sh123/arduino_uno_pet_puller/extras/cad_petalot/guide-base.stl

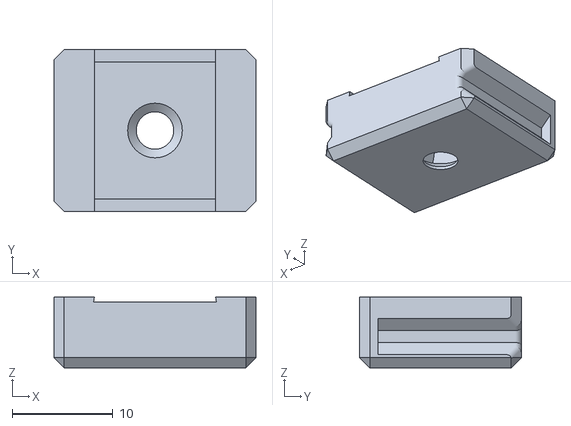
[picture p15: CAD file, 2025-09-10]
extras/cad_petalot/guide-base.stl
20.0 x 16.0 x 7.00
