sh123/arduino_uno_pet_puller/extras/cad_petalot/cable-clamp.stl

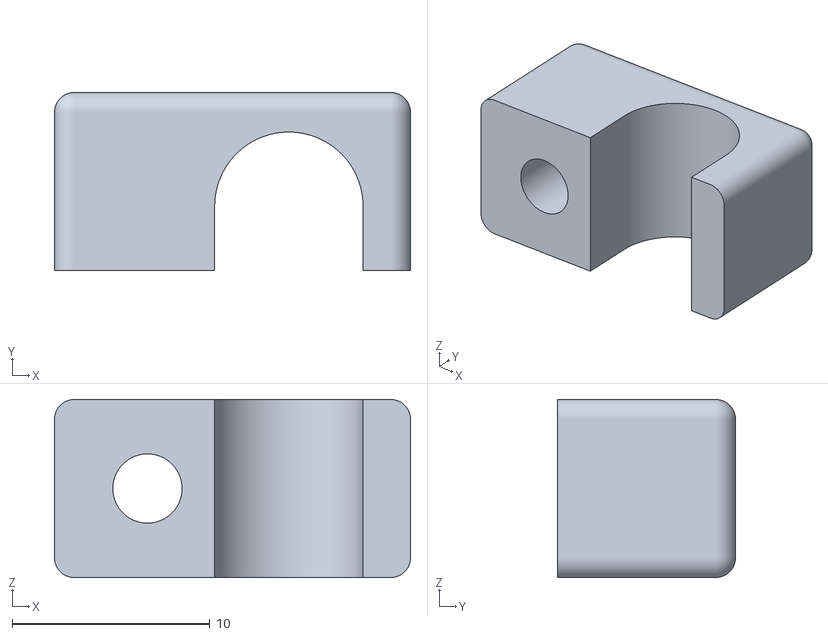
[picture p16: CAD file, 2025-09-10]
extras/cad_petalot/cable-clamp.stl
18.0 x 9.00 x 9.00
