sh123/arduino_uno_pet_puller/extras/cad_petalot/pulley.stl

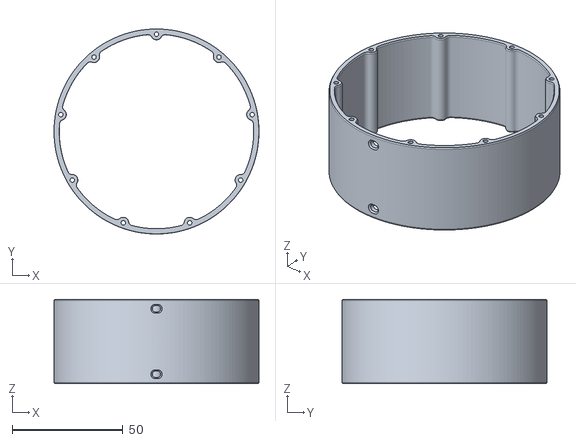
[picture p17: CAD file, 2025-09-10]
extras/cad_petalot/pulley.stl
92.4 x 92.4 x 38.0
