sh123/arduino_uno_pet_puller/extras/cad_petalot/filament-sensor-cap.stl

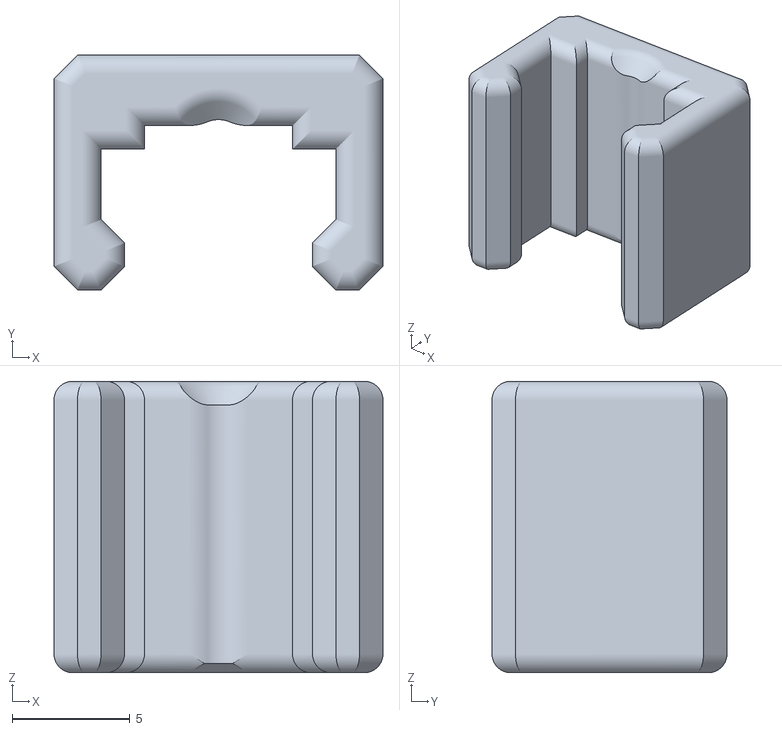
[picture p18: CAD file, 2025-09-10]
extras/cad_petalot/filament-sensor-cap.stl
14.0 x 10.0 x 12.4
