sh123/arduino_uno_pet_puller/extras/cad_petalot/filament-sensor-body.stl

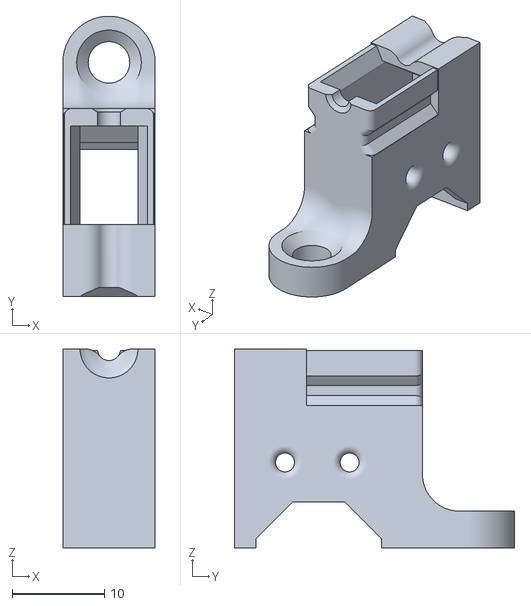
[picture p19: CAD file, 2025-09-10]
extras/cad_petalot/filament-sensor-body.stl
10.0 x 30.4 x 21.6
