sh123/arduino_uno_pet_puller/extras/cad_petalot/spacer-8.stl

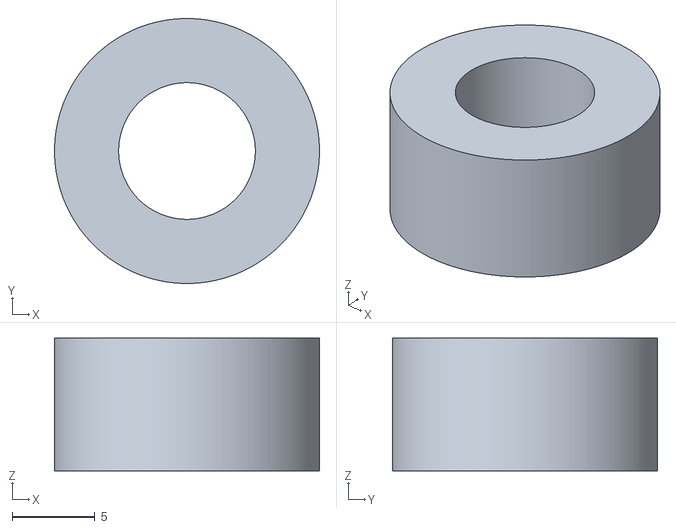
[picture p20: CAD file, 2025-09-10]
extras/cad_petalot/spacer-8.stl
16.0 x 16.0 x 8.00
