sh123/arduino_uno_pet_puller/extras/cad_petalot/body-2.stl

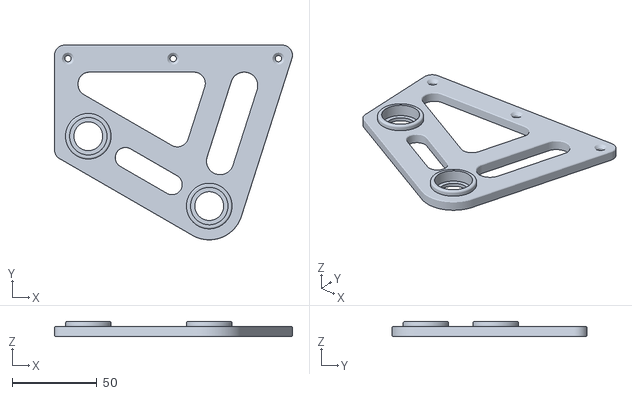
[picture p21: CAD file, 2025-09-10]
extras/cad_petalot/body-2.stl
140.8 x 115.2 x 9.00
